jayflatland/HighFrequencyTwister/CAD Drawings/Phase 2 Speedster/Fixed Claw.FCStd

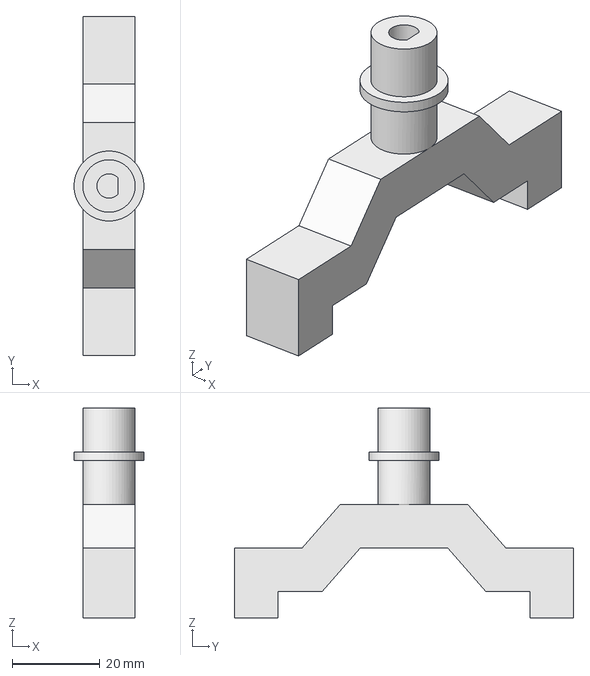
[picture p15: CAD file, 2017-01-15]
CAD Drawings/Phase 2 Speedster/Fixed Claw.FCStd
16.0 x 77.5 x 48.0 mm
