jayflatland/HighFrequencyTwister/CAD Drawings/Phase 3 Claw/Claw.FCStd

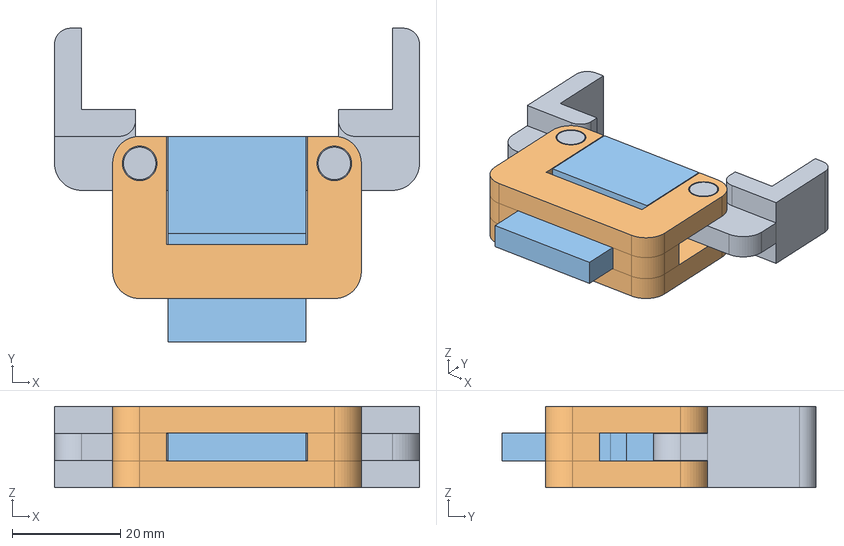
[picture p16: CAD file, 2017-01-15]
CAD Drawings/Phase 3 Claw/Claw.FCStd
67.5 x 58.0 x 15.0 mm
Claws
Arms
