jayflatland/HighFrequencyTwister/CAD Drawings/Phase 4 Center Drive Redux/Notched Center Square.FCStd

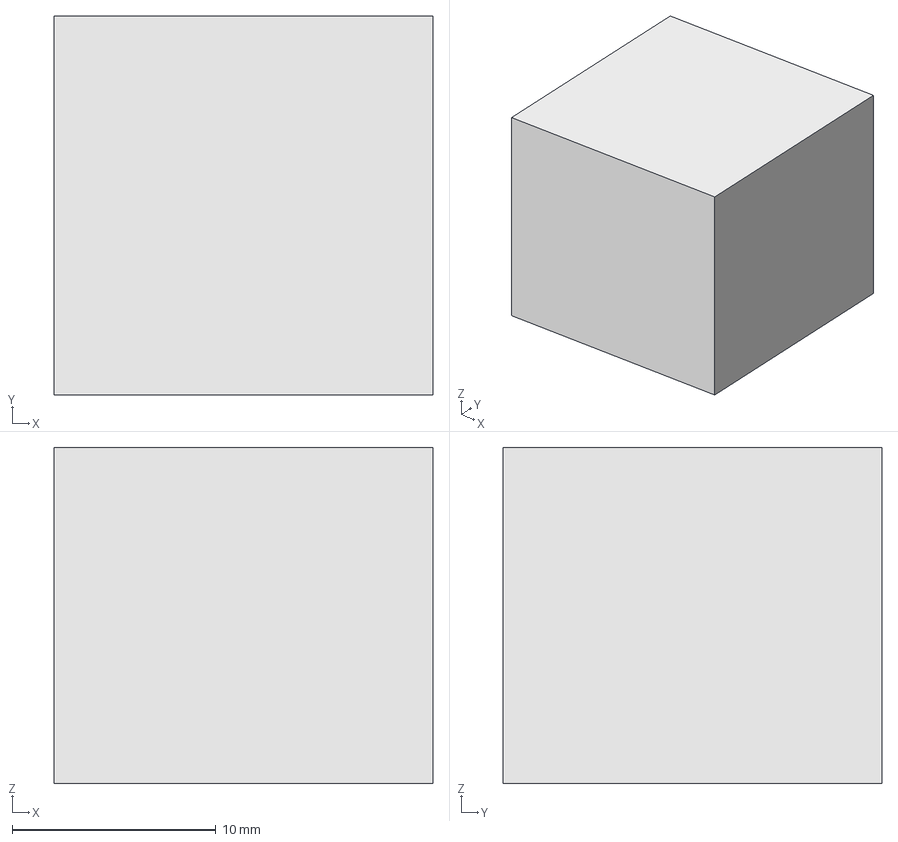
[picture p17: CAD file, 2017-01-15]
CAD Drawings/Phase 4 Center Drive Redux/Notched Center Square.FCStd
18.6 x 18.6 x 16.5 mm
