jayflatland/HighFrequencyTwister/CAD Drawings/Phase 5 Claw/Claw5 - Arms.stl

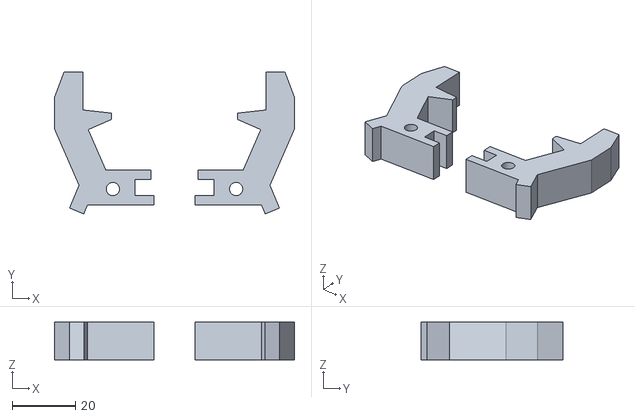
[picture p18: CAD file, 2017-01-15]
CAD Drawings/Phase 5 Claw/Claw5 - Arms.stl
75.9 x 44.9 x 12.0
