jayflatland/HighFrequencyTwister/CAD Drawings/Camera Mounts/Lower Camera Mount.FCStd

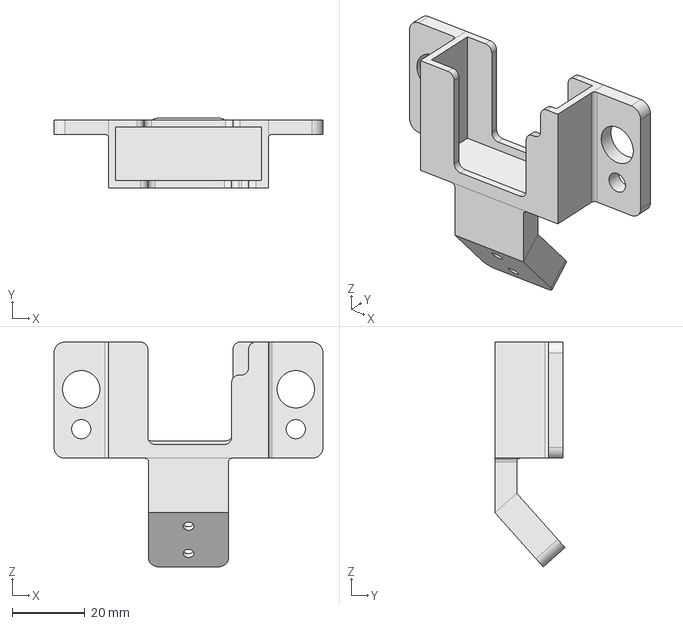
[picture p19: CAD file, 2017-01-15]
CAD Drawings/Camera Mounts/Lower Camera Mount.FCStd
74.1 x 19.3 x 61.9 mm
