jayflatland/HighFrequencyTwister/CAD Drawings/Phase 1 Prototype/Rubiks Center Square Foot 3 - Capless Drive.FCStd

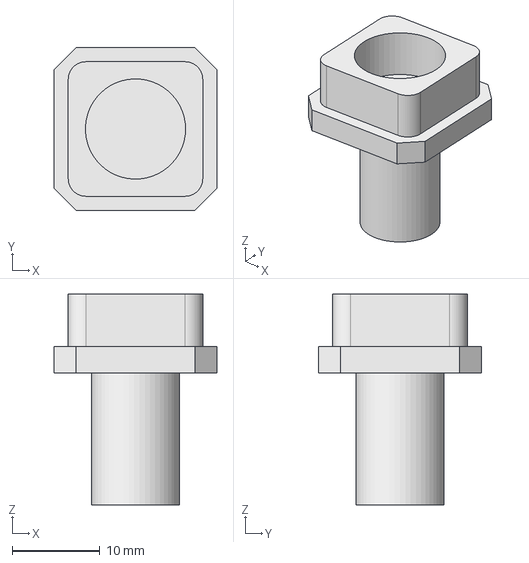
[picture p20: CAD file, 2017-01-15]
CAD Drawings/Phase 1 Prototype/Rubiks Center Square Foot 3 - Capless Drive.FCStd
18.5 x 18.5 x 24.0 mm
