jayflatland/HighFrequencyTwister/CAD Drawings/Phase 2 Speedster/Solenoid Boot.FCStd

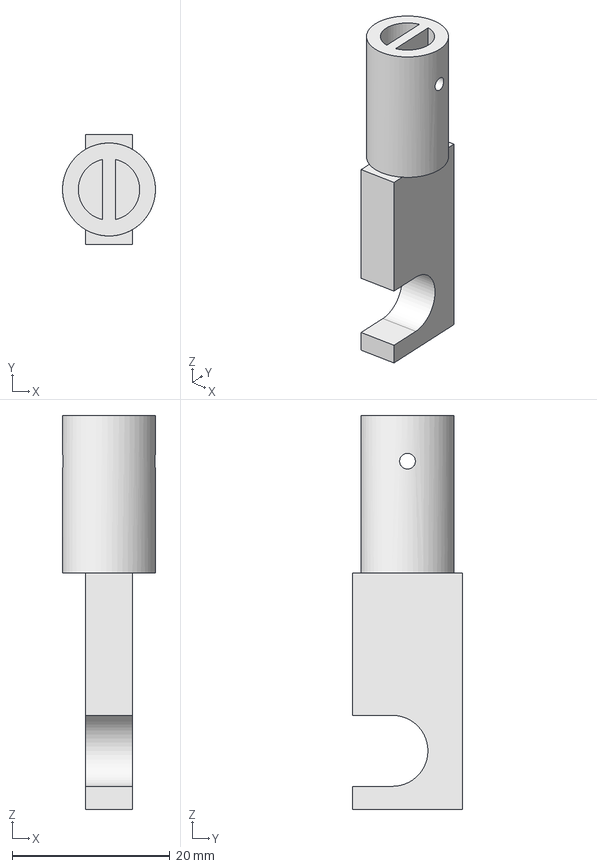
[picture p21: CAD file, 2017-01-15]
CAD Drawings/Phase 2 Speedster/Solenoid Boot.FCStd
11.8 x 14.0 x 50.0 mm
