jayflatland/HighFrequencyTwister/CAD Drawings/Phase 3 Claw/Peg.FCStd

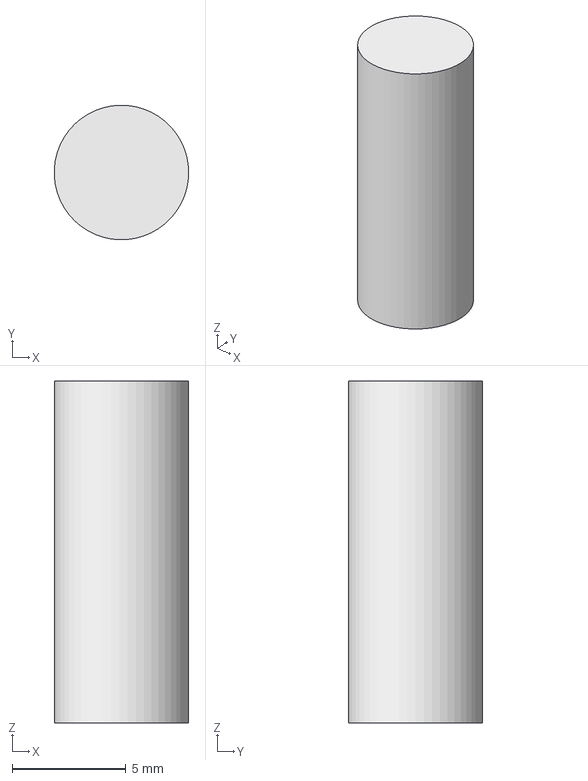
[picture p22: CAD file, 2017-01-15]
CAD Drawings/Phase 3 Claw/Peg.FCStd
5.89 x 5.90 x 15.0 mm
