jayflatland/HighFrequencyTwister/CAD Drawings/Phase 4 Center Drive Redux/Drill Template.FCStd

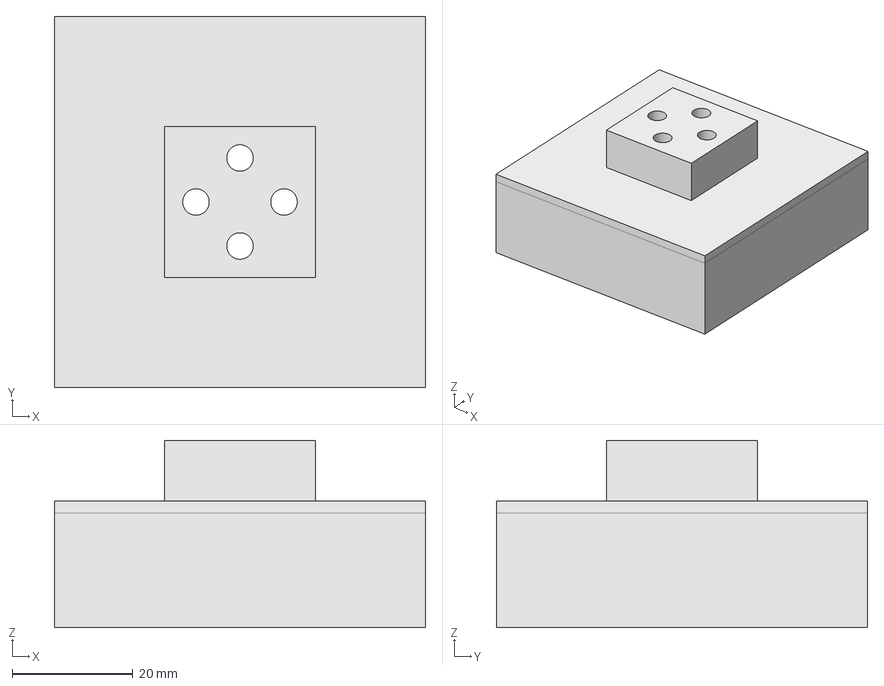
[picture p23: CAD file, 2017-01-15]
CAD Drawings/Phase 4 Center Drive Redux/Drill Template.FCStd
61.5 x 61.5 x 31.0 mm
