jayflatland/HighFrequencyTwister/CAD Drawings/Phase 5 Claw/Claw5 - Rocker.stl

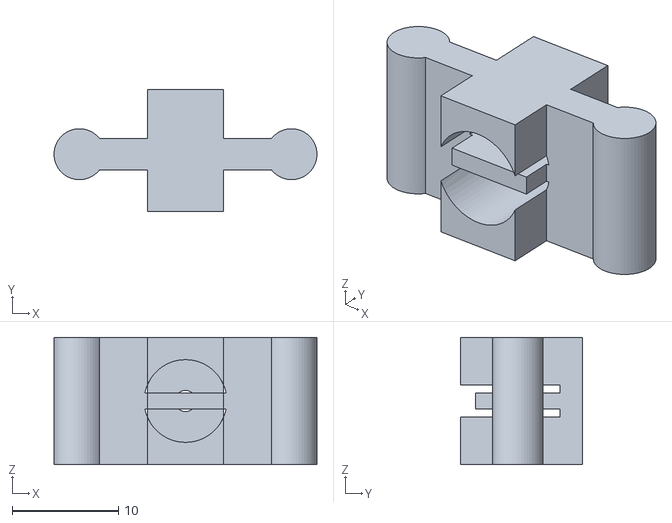
[picture p24: CAD file, 2017-01-15]
CAD Drawings/Phase 5 Claw/Claw5 - Rocker.stl
24.8 x 11.5 x 12.0
