jayflatland/HighFrequencyTwister/CAD Drawings/Phase 1 Prototype/Rubiks Frame Bottom Top Small Steppers.FCStd

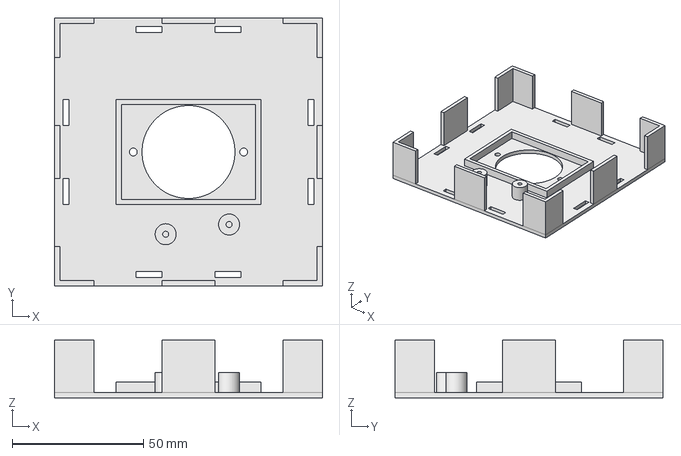
[picture p25: CAD file, 2017-01-15]
CAD Drawings/Phase 1 Prototype/Rubiks Frame Bottom Top Small Steppers.FCStd
102.0 x 102.0 x 22.0 mm
