jayflatland/HighFrequencyTwister/CAD Drawings/Phase 3 Claw/Claw 2.FCStd

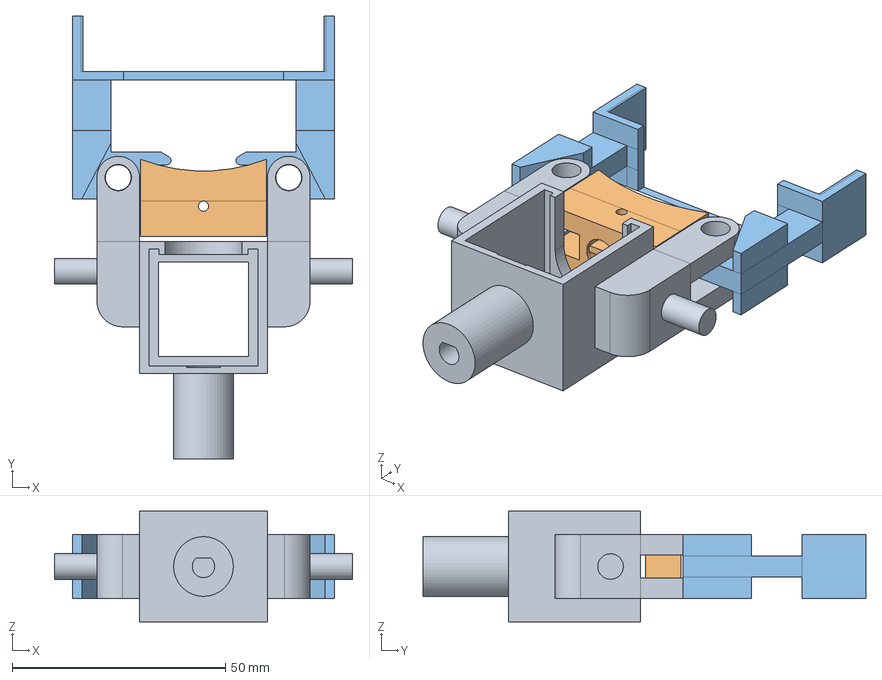
[picture p26: CAD file, 2017-01-15]
CAD Drawings/Phase 3 Claw/Claw 2.FCStd
70.0 x 103.9 x 26.0 mm
BRACKET
PUSHBOX
FEET
