jayflatland/HighFrequencyTwister/CAD Drawings/Phase 3 Claw/Claw 2 - Bracket.stl

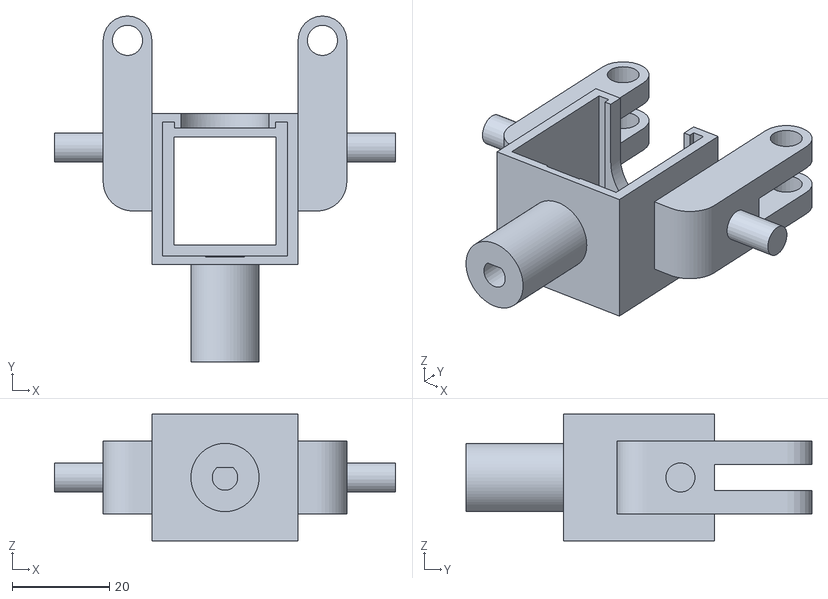
[picture p27: CAD file, 2017-01-15]
CAD Drawings/Phase 3 Claw/Claw 2 - Bracket.stl
70.0 x 71.0 x 26.0
