jayflatland/HighFrequencyTwister/CAD Drawings/Phase 4 Center Drive Redux/Five Motor Frame.FCStd

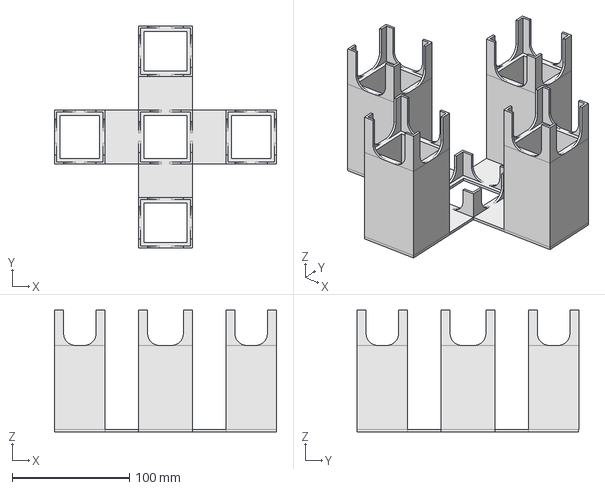
[picture p28: CAD file, 2017-01-15]
CAD Drawings/Phase 4 Center Drive Redux/Five Motor Frame.FCStd
189.4 x 189.4 x 103.7 mm
