jayflatland/HighFrequencyTwister/CAD Drawings/Phase 5 Claw/Claw5 - Calibration Pole.FCStd

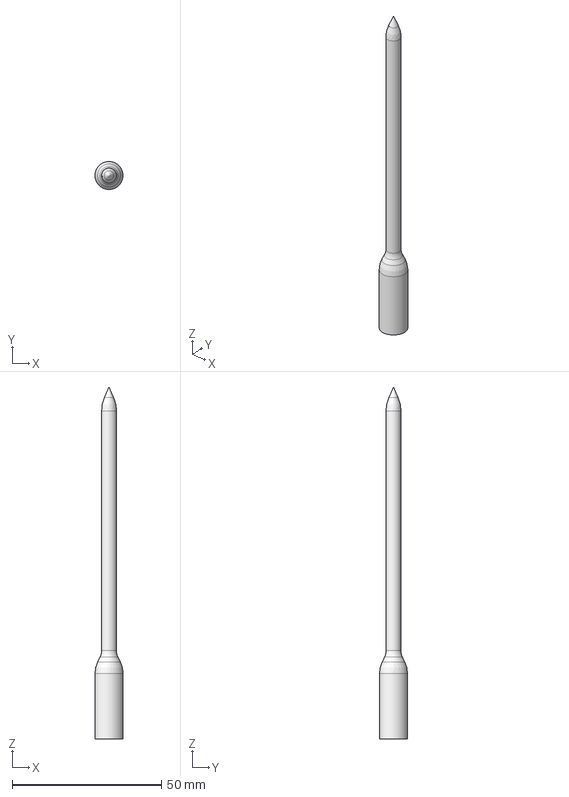
[picture p29: CAD file, 2017-01-15]
CAD Drawings/Phase 5 Claw/Claw5 - Calibration Pole.FCStd
9.39 x 9.40 x 118.0 mm
