jayflatland/HighFrequencyTwister/CAD Drawings/Phase 1 Prototype/Small Stepper Bracket Template.STL

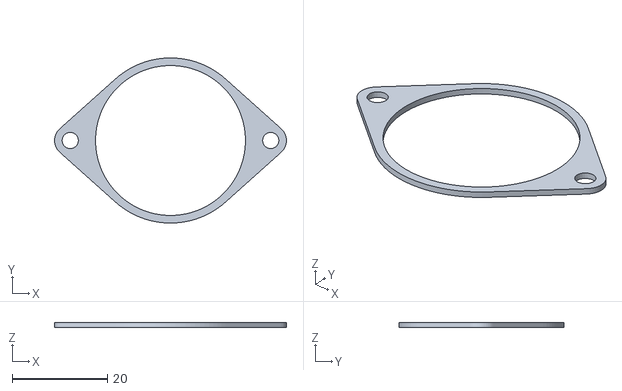
[picture p30: CAD file, 2017-01-15]
CAD Drawings/Phase 1 Prototype/Small Stepper Bracket Template.STL
48.6 x 34.6 x 1.00
