jayflatland/HighFrequencyTwister/CAD Drawings/Phase 2 Speedster/Single Part Hinge Test.FCStd

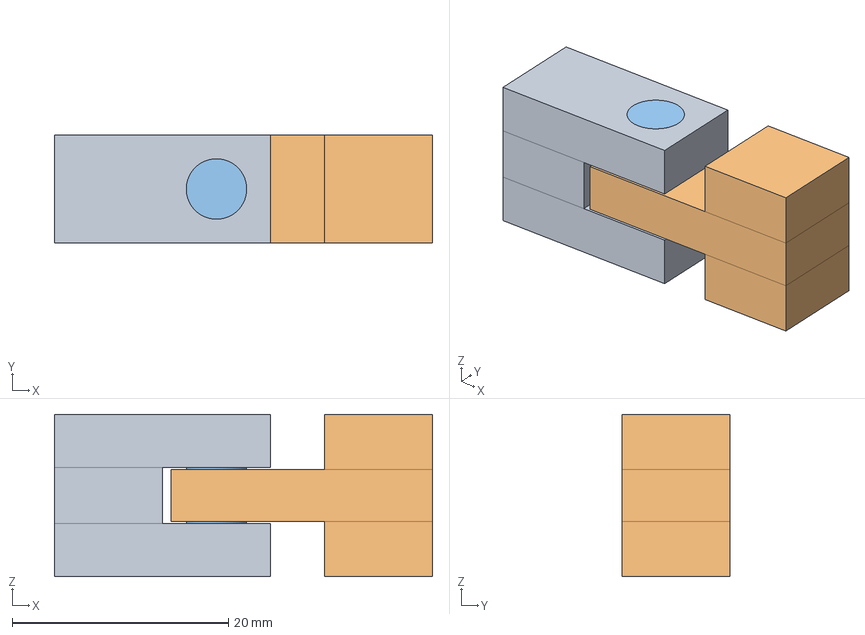
[picture p31: CAD file, 2017-01-15]
CAD Drawings/Phase 2 Speedster/Single Part Hinge Test.FCStd
35.0 x 10.0 x 15.0 mm
