jayflatland/HighFrequencyTwister/CAD Drawings/Phase 3 Claw/Claw 2 - Feet.stl

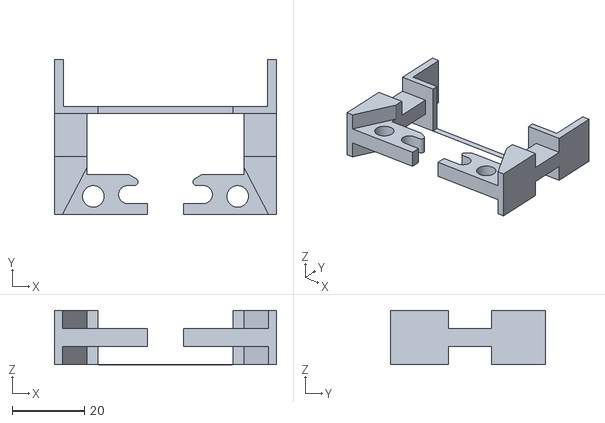
[picture p32: CAD file, 2017-01-15]
CAD Drawings/Phase 3 Claw/Claw 2 - Feet.stl
61.5 x 42.9 x 15.0
