jayflatland/HighFrequencyTwister/CAD Drawings/Phase 1 Prototype/Rubiks Frame Side Small Steppers.FCStd

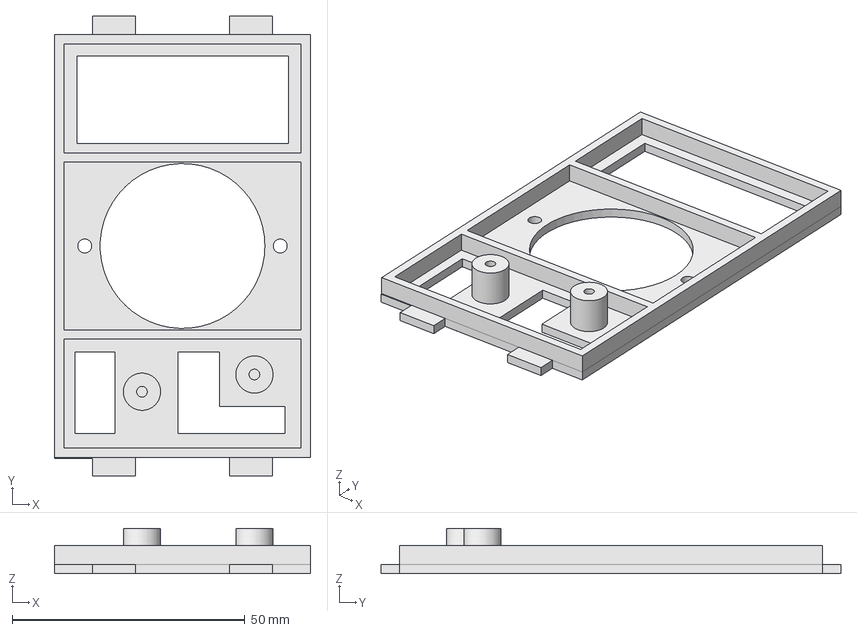
[picture p33: CAD file, 2017-01-15]
CAD Drawings/Phase 1 Prototype/Rubiks Frame Side Small Steppers.FCStd
55.0 x 98.8 x 9.70 mm
