jayflatland/HighFrequencyTwister/CAD Drawings/Phase 2 Speedster/Push Ring Bottom.stl

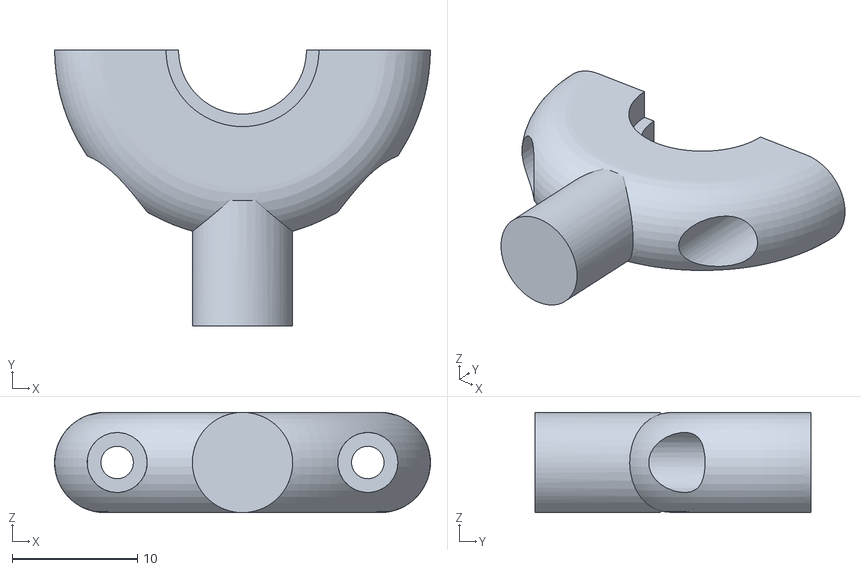
[picture p34: CAD file, 2017-01-15]
CAD Drawings/Phase 2 Speedster/Push Ring Bottom.stl
30.0 x 22.0 x 8.00
