jayflatland/HighFrequencyTwister/CAD Drawings/Phase 3 Claw/Claw 2 - Pushbox.stl

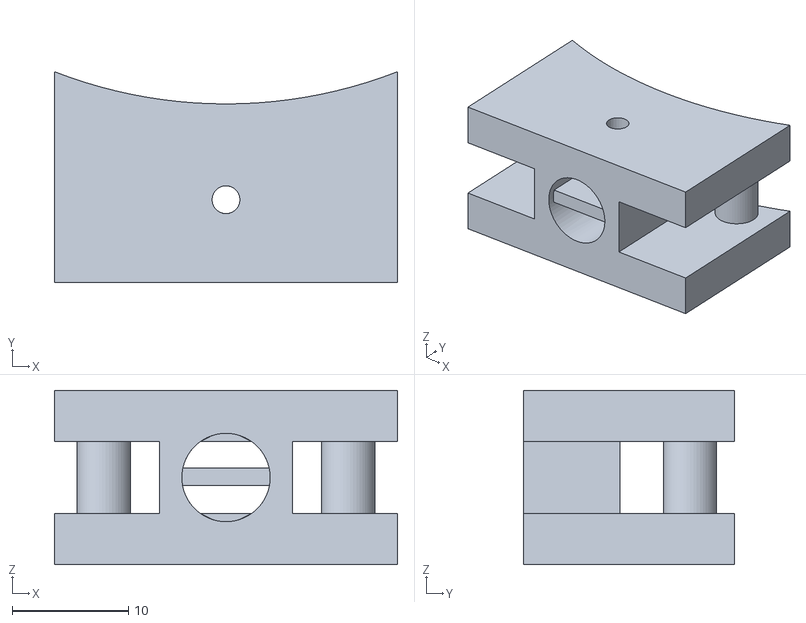
[picture p35: CAD file, 2017-01-15]
CAD Drawings/Phase 3 Claw/Claw 2 - Pushbox.stl
29.5 x 18.1 x 15.0
