jayflatland/HighFrequencyTwister/CAD Drawings/Phase 4 Center Drive Redux/Sixth Motor Frame.FCStd

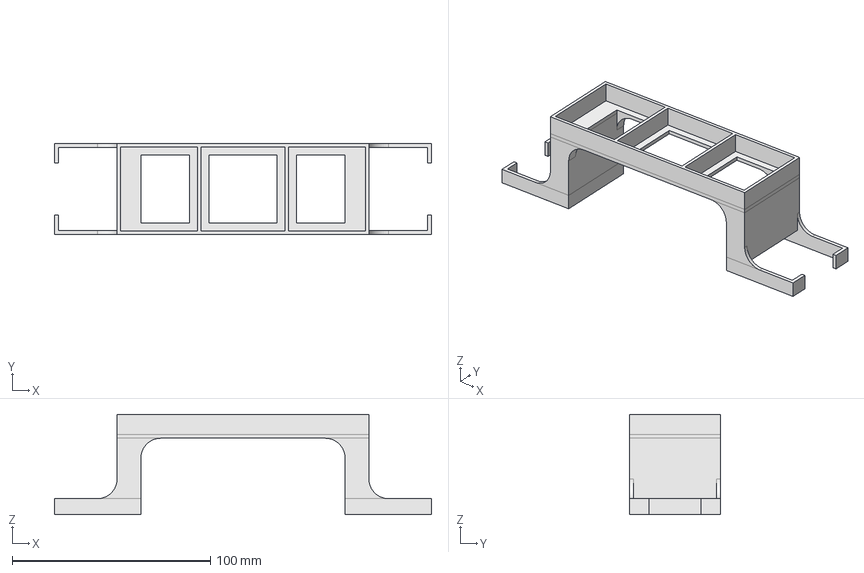
[picture p36: CAD file, 2017-01-15]
CAD Drawings/Phase 4 Center Drive Redux/Sixth Motor Frame.FCStd
190.2 x 46.0 x 50.5 mm
