jayflatland/HighFrequencyTwister/CAD Drawings/Phase 1 Prototype/Rubiks Motor Bottom Bracket.FCStd

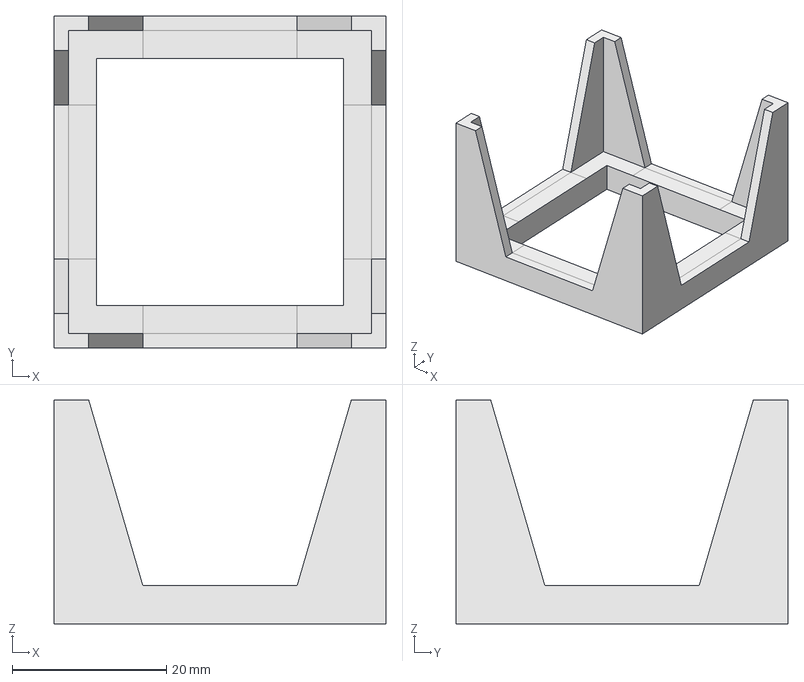
[picture p37: CAD file, 2017-01-15]
CAD Drawings/Phase 1 Prototype/Rubiks Motor Bottom Bracket.FCStd
43.0 x 43.0 x 29.0 mm
