jayflatland/HighFrequencyTwister/CAD Drawings/Phase 2 Speedster/Push Ring.FCStd

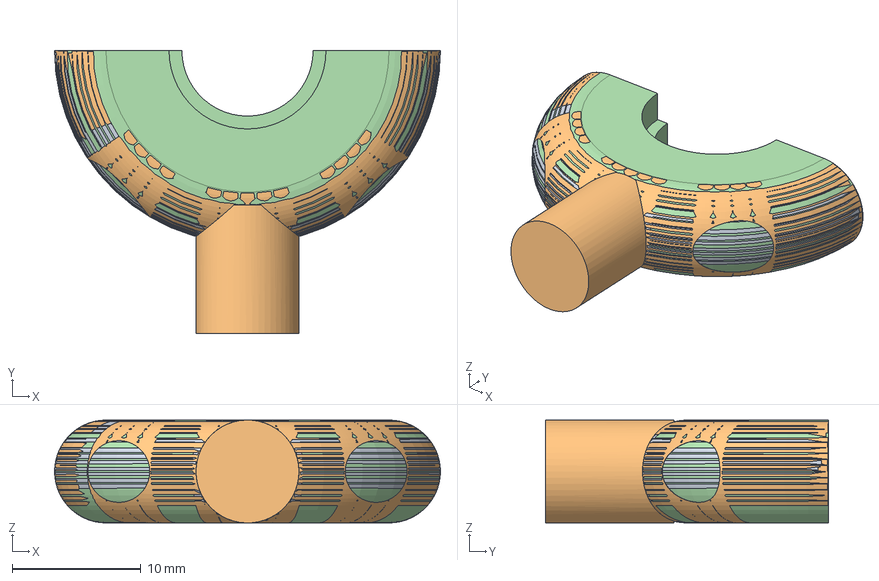
[picture p38: CAD file, 2017-01-15]
CAD Drawings/Phase 2 Speedster/Push Ring.FCStd
30.0 x 22.0 x 8.00 mm
Top
Bottom
