jayflatland/HighFrequencyTwister/CAD Drawings/Phase 4 Center Drive Redux/Positioning Calibrator.FCStd

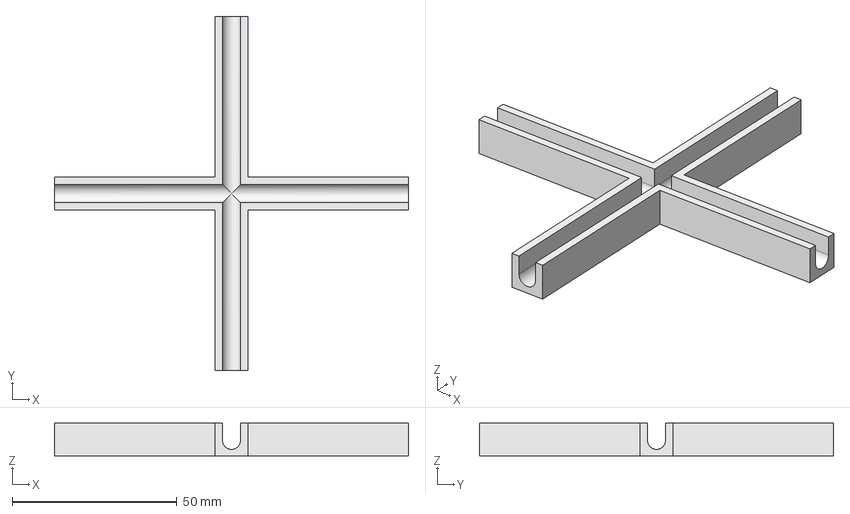
[picture p39: CAD file, 2017-01-15]
CAD Drawings/Phase 4 Center Drive Redux/Positioning Calibrator.FCStd
107.5 x 107.5 x 10.0 mm
