jayflatland/HighFrequencyTwister/CAD Drawings/Phase 2 Speedster/Push Lever.FCStd

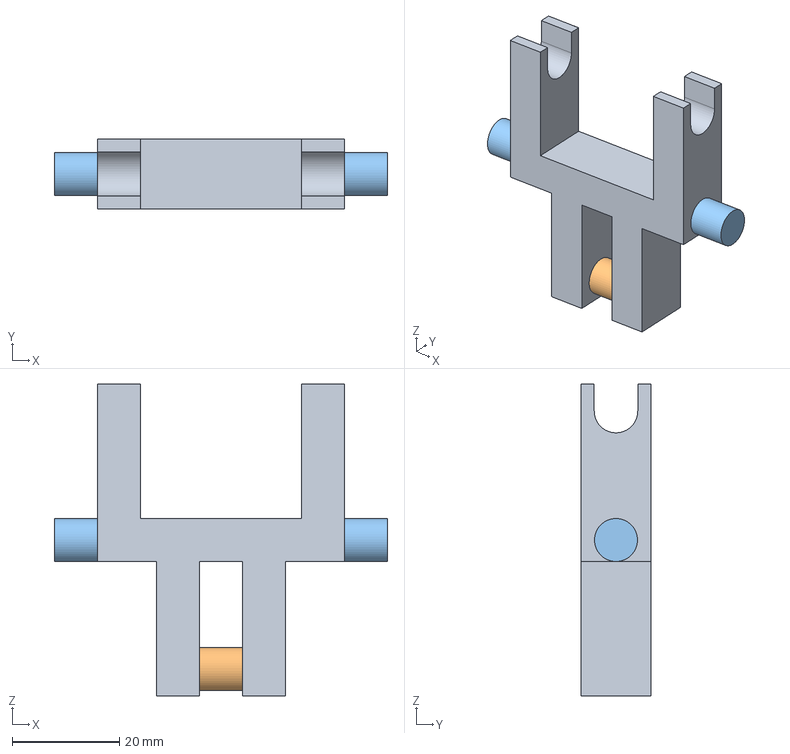
[picture p40: CAD file, 2017-01-15]
CAD Drawings/Phase 2 Speedster/Push Lever.FCStd
62.0 x 13.0 x 58.0 mm
