jayflatland/HighFrequencyTwister/CAD Drawings/Phase 4 Center Drive Redux/Center Drive Test 1.FCStd

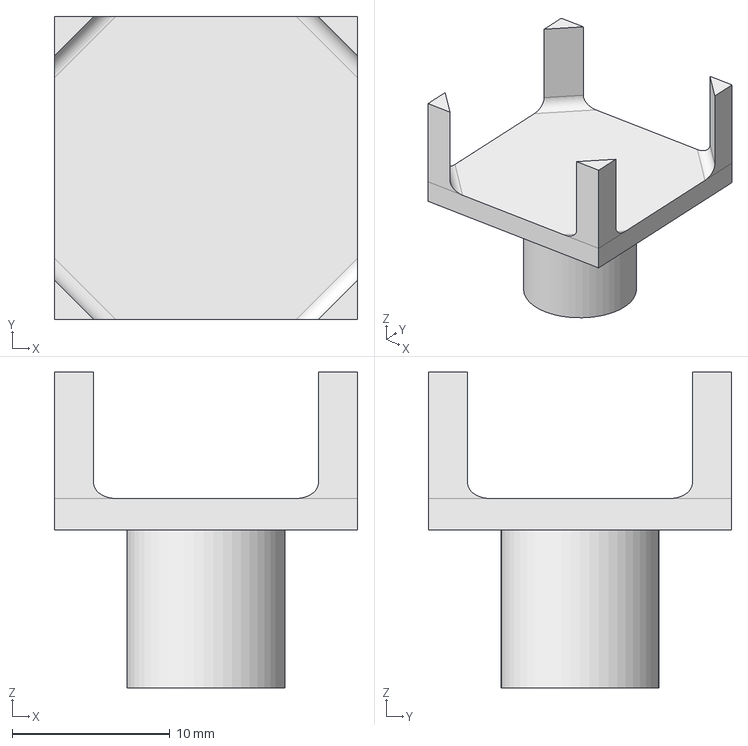
[picture p41: CAD file, 2017-01-15]
CAD Drawings/Phase 4 Center Drive Redux/Center Drive Test 1.FCStd
19.2 x 19.2 x 20.0 mm
