jayflatland/HighFrequencyTwister/CAD Drawings/Phase 1 Prototype/Small Stepper Drive Shaft Test Knob.STL

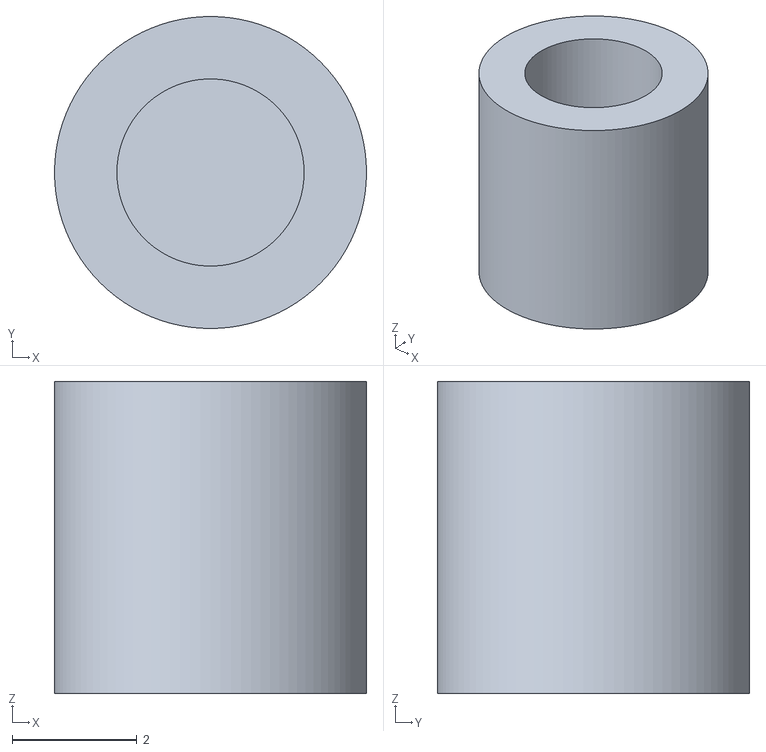
[picture p42: CAD file, 2017-01-15]
CAD Drawings/Phase 1 Prototype/Small Stepper Drive Shaft Test Knob.STL
5.00 x 5.00 x 5.00
