jayflatland/HighFrequencyTwister/CAD Drawings/Phase 2 Speedster/Solenoid Tray Test.FCStd

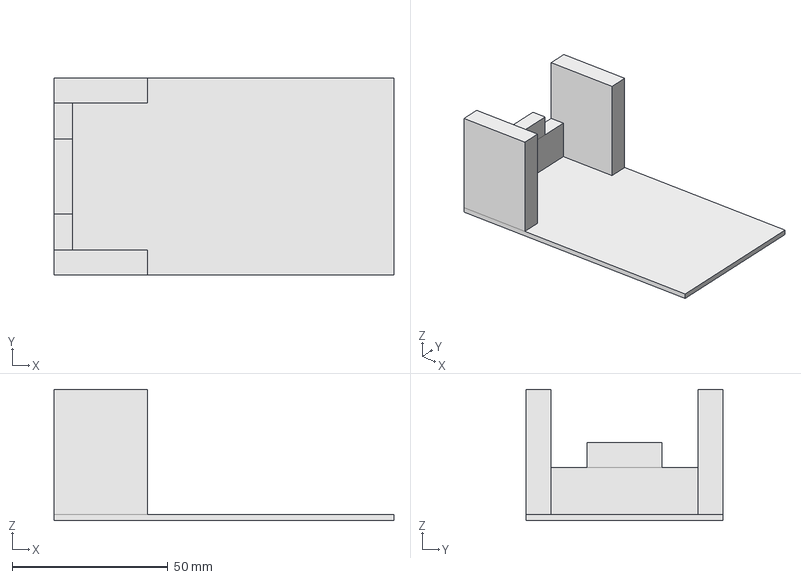
[picture p43: CAD file, 2017-01-15]
CAD Drawings/Phase 2 Speedster/Solenoid Tray Test.FCStd
109.0 x 63.0 x 42.0 mm
