jayflatland/HighFrequencyTwister/CAD Drawings/Phase 4 Center Drive Redux/Drilled Cube Drive Bit.FCStd

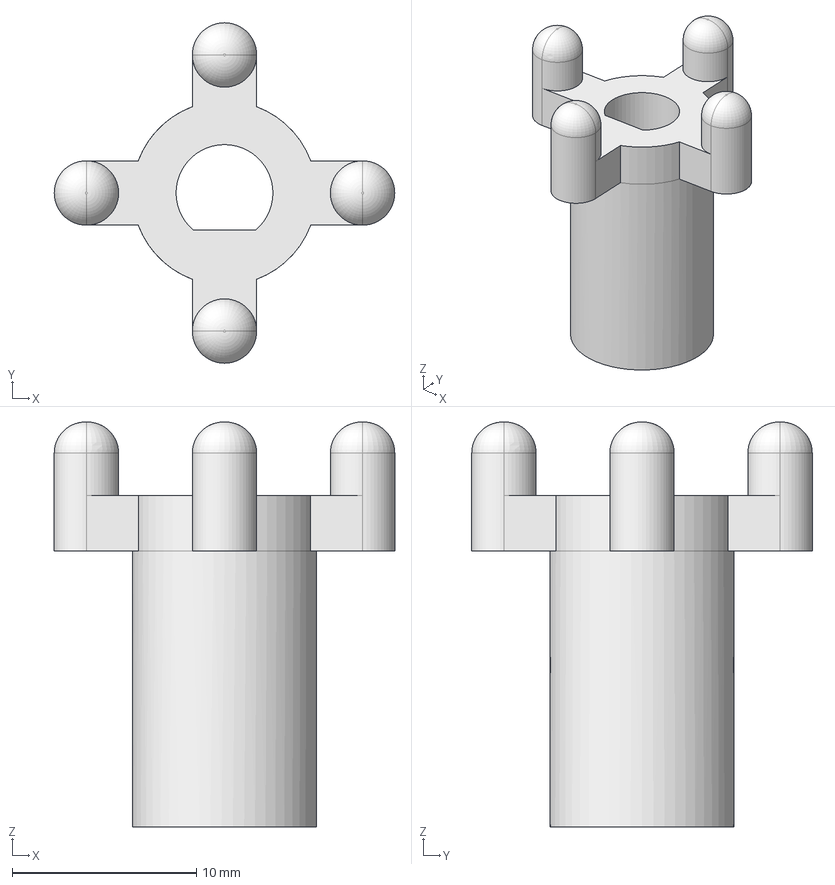
[picture p44: CAD file, 2017-01-15]
CAD Drawings/Phase 4 Center Drive Redux/Drilled Cube Drive Bit.FCStd
18.5 x 18.5 x 22.0 mm
