jayflatland/HighFrequencyTwister/CAD Drawings/Phase 1 Prototype/Rubiks Motor Side Bracket.FCStd

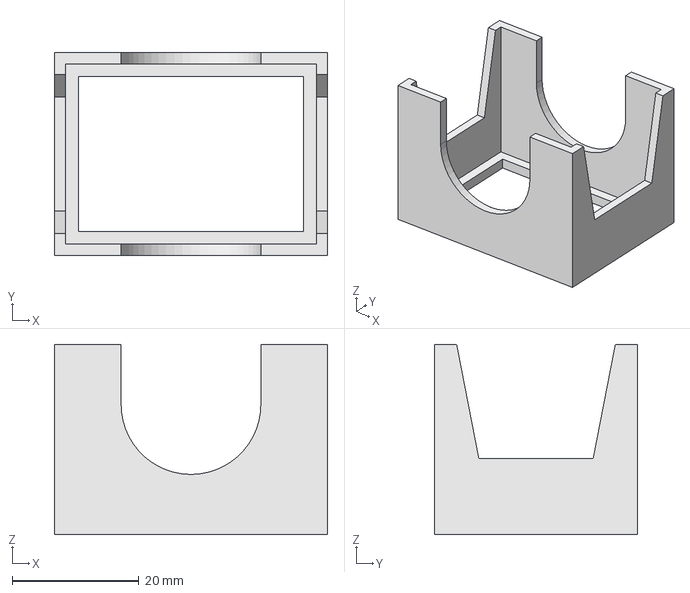
[picture p45: CAD file, 2017-01-15]
CAD Drawings/Phase 1 Prototype/Rubiks Motor Side Bracket.FCStd
43.0 x 32.0 x 30.0 mm
