jayflatland/HighFrequencyTwister/CAD Drawings/Phase 1 Prototype/Small Stepper.STL

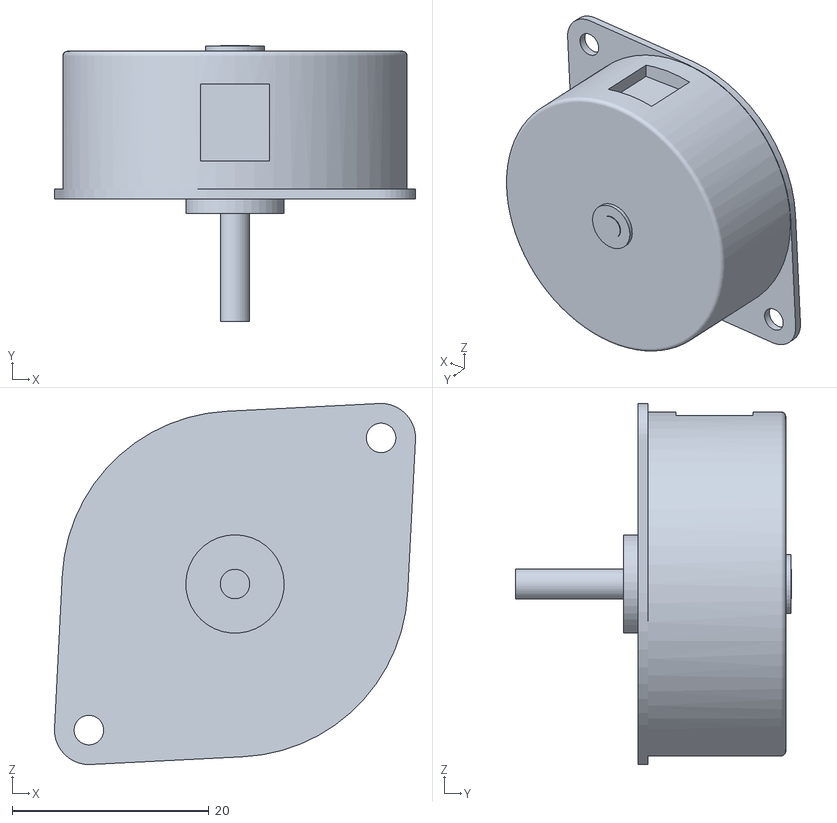
[picture p46: CAD file, 2017-01-15]
CAD Drawings/Phase 1 Prototype/Small Stepper.STL
36.7 x 28.1 x 36.7
