jayflatland/HighFrequencyTwister/CAD Drawings/Phase 1 Prototype/Rubiks Robot Frame.FCStd

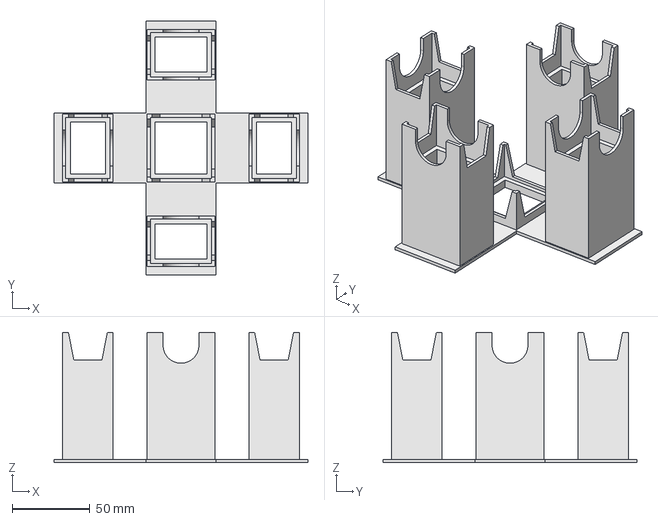
[picture p47: CAD file, 2017-01-15]
CAD Drawings/Phase 1 Prototype/Rubiks Robot Frame.FCStd
163.0 x 163.0 x 83.6 mm
