jayflatland/HighFrequencyTwister/CAD Drawings/Phase 1 Prototype/Rubiks Center Square Foot.FCStd

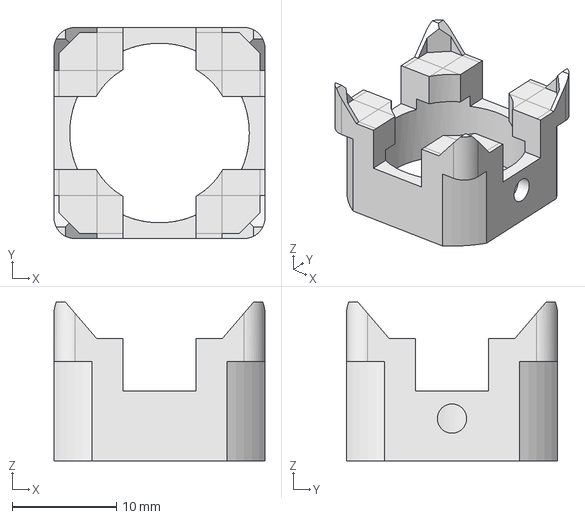
[picture p48: CAD file, 2017-01-15]
CAD Drawings/Phase 1 Prototype/Rubiks Center Square Foot.FCStd
20.2 x 20.2 x 15.2 mm
