jayflatland/HighFrequencyTwister/ArduinoUno_Phase3_Center_Drive/delay_table.h

static const int delays90_1[] = {
     2250,   //  800 deg/sec
     1836,   //  980 deg/sec
     1597,   // 1126 deg/sec
     1434,   // 1254 deg/sec
     1314,   // 1369 deg/sec
     1220,   // 1474 deg/sec
     1144,   // 1572 deg/sec
     1081,   // 1663 deg/sec
     1028,   // 1750 deg/sec
      982,   // 1832 deg/sec
      941,   // 1911 deg/sec
      906,   // 1986 deg/sec
      874,   // 2059 deg/sec
      845,   // 2129 deg/sec
      819,   // 2196 deg/sec
      795,   // 2262 deg/sec
      773,   // 2325 deg/sec
      753,   // 2387 deg/sec
      735,   // 2448 deg/sec
      718,   // 2506 deg/sec
      701,   // 2564 deg/sec
      686,   // 2620 deg/sec
      672,   // 2675 deg/sec
      659,   // 2729 deg/sec
      647,   // 2782 deg/sec
      635,   // 2833 deg/sec
      646,   // 2782 deg/sec
      659,   // 2731 deg/sec
      672,   // 2678 deg/sec
      685,   // 2624 deg/sec
      700,   // 2569 deg/sec
      716,   // 2513 deg/sec
      732,   // 2456 deg/sec
      750,   // 2397 deg/sec
      769,   // 2337 deg/sec
      790,   // 2276 deg/sec
      813,   // 2213 deg/sec
      837,   // 2147 deg/sec
      864,   // 2080 deg/sec
      894,   // 2011 deg/sec
      927,   // 1940 deg/sec
      964,   // 1865 deg/sec
     1006,   // 1788 deg/sec
     1053,   // 1708 deg/sec
     1108,   // 1623 deg/sec
     1172,   // 1535 deg/sec
     1248,   // 1441 deg/sec
     1341,   // 1341 deg/sec
     1458,   // 1234 deg/sec
     1610,   // 1117 deg/sec
};

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
    case 5: return delays90_5[ i ];
    }
}

static inline int getDelay180( int i ) {
    switch( speed ) {
    default:
    case 1: return delays180_1[ i ];
    case 3: return delays180_3[ i ];
    case 4: return delays180_4[ i ];
    case 5: return delays180_5[ i ];
    }
}
