jayflatland/HighFrequencyTwister/Phase_2_Arduino_Code/delay_table.h

400,
334,
287,
251,
223,
201,
183,
168,
155,
144,
134,
126,
119,
112,
106,
101,
96,
92,
88,
84,
81,
78,
75,
72,
70,
67,
65,
63,
61,
59,
58,
56,
55,
53,
52,
51,
49,
48,
47,
46,
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
